qsbird/smart-apo/hardware/revA2/LDO_CAPACITOR_REVIEW_CN.md

# U7输出电容角色与候选布局复核 · 2026-09-23

## 由项目文件确认

本轮读取正式网表与BOM，U7为TPS7A0233PDBVR；C3=100nF、C9=1µF、C10=1µF。C10及C3接3V3/GND，U7.5为3V3输出；C9是输入侧容量。此前讨论将C3当作唯一LDO输出电容不准确，不能据C3移位单独推定稳压失效。

用KiCad Python只读比较正式板与MOSI try6：U7.5到C10.1的显式F.Cu轨段图长度均为1.436347763mm，C10的值/位置/网络保持。C3在try6图中为11.659789mm；正式板的简化端点图没有把中途搭接拆节点而返回null，null不是断路证据，实际连通须以官方DRC与pcbnew连接图为准。该度量不含焊盘内路径、铺铜、过孔和完整返回回路，不是阻抗/ESR/稳定性测量。脚本、散列与结果见validation/revA2_ldo_cap_review。

## 原厂条件及仍缺证据

[TI TPS7A02数据手册SBVS277C Rev.C](https://www.ti.com/lit/ds/symlink/tps7a02.pdf)第3/5页规定输出有效电容至少0.5µF，推荐1µF或更大陶瓷电容并靠近OUT；第23页提醒有效容量受工作电压、温度影响。不能只凭BOM的1µF标称值判定通过。

当前C10仍为Generic MLCC、无明确采购MPN与偏压/温度曲线。必须确认所选C10在实际3.3V和应用温度/容差下的有效容量及近端返回路径，并做板上启动/负载瞬态等检查。当前只确认近端名义电容支路没有因C3移动而消失，未完成稳定性/瞬态验证。

本轮不改元件值、BOM采购后缀、正式PCB或固件。MOSI try6仍为独立候选，不能把本报告当作采用或制造放行证据。
