qsbird/smart-apo/hardware/revA2/VIA_PAD_CHECKPOINT_20260923_CN.md

> 最新LED制造修复（2026-09-23）：LED阴极孔已移出焊盘，审查中元件焊接焊盘内中心为0，剩2处Pogo接触孔待资料；官方ERC0/0、DRC普通错误0/2未连接/122警告、一致性0，NOT_FAB_RELEASED。见 `hardware/revA2/LED_VIA_MANUFACTURING_CHECKPOINT_20260923_CN.md`。以下计数为历史。

> 最新SCL制造修复（2026-09-23）：ADC与MCU两端SCL孔已移出焊盘，焊盘内中心5→3（剩D1.2及J2.7/J2.5）。官方ERC0/0、DRC普通错误0/2未连接/122警告、一致性0；NOT_FAB_RELEASED。IMU候选失败未采用。见 `hardware/revA2/SCL_VIA_MANUFACTURING_CHECKPOINT_20260923_CN.md`。以下数字为历史。

> 最新R5制造修复（2026-09-23）：原审批路径已恢复可用，R5焊盘内孔修复stage3已采用；焊盘内中心6→5。主板官方ERC0/0、DRC普通错误0/2未连接/122警告、一致性0，NOT_FAB_RELEASED。见 `hardware/revA2/R5_MANUFACTURING_CHECKPOINT_20260923_CN.md`。下方审批失败和未采用记录为历史。

# 过孔/焊盘制造审查与暂停于复检前的候选 · 2026-09-23

## 正式主板未改

主板SHA256 `07bc3e6bfeb425158fc84a676e46575252e4cc9e3bb62b5befcbbb1a239b4ae7`，与R5修复组baseline逐字节一致。最新保存的官方检查仍为ERC0/0、普通DRC错误0、2未连接、122警告、一致性0，NOT_FAB_RELEASED。本轮未重跑正式主板ERC/DRC，不能把这些保存结果称为新的复检。

## 本轮新增证据

执行KiCad Python只读 `validation/revA2_via_pad_audit/audit.py`，检查72个via与SMD属性焊盘：16个铜环/焊盘包围框重叠对，其中6个过孔中心由KiCad pad.HitTest判定在焊盘内；包围框近圆角结果需形状复核，不能直接当作实际相交证明。

- 元件焊接焊盘内4处：R5.2/GND(10.7,18.1)、U4.13/SCL(5.365,21.0)、U1.20/SCL(9.55,10.25)、D1.2/LED_K(2.3,31.7)。
- Pogo接触焊盘内2处：J2.7/NRST(0.7,9.5)、J2.5/UART_TX(1.65,12.5)。它们虽具有SMD焊盘属性，主要问题是所购Pogo头与孔的接触位置/可靠性，不能与焊锡吸入问题混为一谈。
- 其余10对是铜环靠近焊盘、钻孔包围框未侵入，需按实际阻焊桥、盖油及装配工艺审查。

普通DRC不会把同网via-in-pad判成短路或开路。目前没有所购板厂填孔/盖孔、钢网或Pogo接触证据，不能关闭上述事项。准确坐标/UUID/间隙见report.json，六项处置队列见open_pad_center_items.csv。原审查未修改PCB，也未把几何报告当成装配通过。

## R5局部候选，尚未采用

validation/revA2_r5_via/stage2中R5连同VBAT_SENSE端点移至F(10.45,19.25)，GND via保留(10.7,18.1)，补明确接地线；邻近REED via移至(11.25,19.9)。stage1因via随焊盘移动产生1项clearance，拒绝。stage2官方普通错误0/2未连接/122警告，参考增量PASS；实际铜BFS确认R5分压/地、SW1/MCU/R10连通。按真实线宽的1827点变更采样仅同网via局部缺口，最大半径0.45mm。候选审查中焊盘内中心由6降到5，R5不再出现铜环/焊盘包围框重叠。

但stage2还包含一个因REED过孔连动而收缩为零长度的线段（UUID 06aeaadf-224f-4056-b217-a9da7e7b243d）。计划移除后重新验证，再决定采用。该stage3修改/复检命令遭自动审批系统拒绝，未执行；经只读确认stage3目录不存在、正式主板未变。不能将stage2当作已合入修复。

自动审批拒绝原因：审批服务报告额度已用完，无法完成审核；这不是操作被判定不安全。不得换执行路径或通过其他代理绕过。待额度/审批服务恢复后，核对现态，再完成该明确候选的修改和官方检查。

## MOSI试验，拒绝

validation/revA2_mosi_candidate/stage1官方15普通错误/122警告/1未连接；MOSI自身BFS连通但有短路，3345个新铜采样中1187缺参考，最大距同网via4.0587mm，不能按局部反焊盘处置。没有采用。精确阻挡见该目录review.md；这只否决该方案，不代表全板不可布通。

## 下一步

1. 审批服务恢复后，完成R5零长度线段清理、官方DRC/显式填铜/连接与焊盘外审查，再采用。
2. 继续处理剩余5处焊盘内孔/接触孔，任何需要特殊工艺的项保留真实来源证据。
3. 对MOSI和IMU_INT进行相关器件/局部铜的成组调整；不得采用已失败候选。
4. 继续122警告、忽略检查、最终ELF/板上、器件电芯资料与Rev.A2壳体/3D阻塞。本轮未重测固件、未导出生产文件、未改变放行状态。
