qsbird/smart-apo/validation/FIELD_TEST_PLAN_CN.md

# Rev.A1 现场闭环验证计划

## 阶段 0：台架

- 两端同步敲击 20 次，验证对时残差 <10 ms；不合格则该航次不进入自动寻参。
- 弹性梁完成 0–2000 g 循环标定，零点漂移、线性误差和回差分别记录；另取样件验证 ≥5 kgf 生存。
- 阿波做人工牵线、轻触、连续拉动、周期摇摆四类动作，每类至少 100 次。

## 阶段 1：静水槽

- 无钩/假饵/真饵三种配置，改变子线长度和配重。
- 造波器或人工做至少三档周期、三档幅度。
- 使用电磁拉线器或伺服在钩端施加可重复脉冲，覆盖 20–800 ms。
- 自动标注后随机抽查不少于 10% 事件。

## 阶段 2：真实水域

- 平静、规则浪、乱浪、横流至少四类水况；每类累计原始记录 ≥2 h。
- 每个航次保留独立测试块，参数不得在同一测试块上反复调整。
- 关键指标：事件召回率、每小时误报数、检测延迟、海况分层性能、电池续航和同步残差。

## 放行标准（建议起点）

- 钩侧机械事件召回率 ≥95%。
- 无人工扰动时误报 ≤2 次/小时。
- 规则浪与乱浪测试块的性能下降均 <10%。
- 参数在下一独立航次仍保持提升，才允许写入阿波默认配置。

“钩侧机械事件”不等同于“鱼咬钩”。若研究目标是鱼种/咬口语义分类，需额外视频或捕获结果标签。
